RebeccaRGB/K130/Arduino/K130/translate.cpp

#include <Arduino.h>
#include <avr/pgmspace.h>
#include "translate.h"

static const unsigned char translation_table[] PROGMEM = {
  0x29, // 0x00 -> 0x29 esc
  0x35, // 0x01 -> 0x35 ` ~
  0x2B, // 0x02 -> 0x2B tab
  0x39, // 0x03 -> 0x39 caps lock
  0xE1, // 0x04 -> 0xE1 left shift
  0xE0, // 0x05 -> 0xE0 left ctrl
  0x85, // 0x06 -> 0x85 numpad ,
  0x59, // 0x07 -> 0x59 numpad 1
  0x5D, // 0x08 -> 0x5D numpad 5
  0x60, // 0x09 -> 0x60 numpad 8
  0x67, // 0x0A -> 0x67 numpad =
  0x81, // 0x0B -> 0x81 volume down
  0x69, // 0x0C -> 0x69 F14
  0x6B, // 0x0D -> 0x6B F16
  0x6D, // 0x0E -> 0x6D F18
  0x6F, // 0x0F -> 0x6F F20
  0x71, // 0x10 -> 0x71 F22
  0x73, // 0x11 -> 0x73 F24
  0x63, // 0x12 -> 0x63 numpad .
  0x5A, // 0x13 -> 0x5A numpad 2
  0x5E, // 0x14 -> 0x5E numpad 6
  0x61, // 0x15 -> 0x61 numpad 9
  0x54, // 0x16 -> 0x54 numpad /
  0x80, // 0x17 -> 0x80 volume up
  0x68, // 0x18 -> 0x68 F13
  0x6A, // 0x19 -> 0x6A F15
  0x6C, // 0x1A -> 0x6C F17
  0x6E, // 0x1B -> 0x6E F19
  0x70, // 0x1C -> 0x70 F21
  0x72, // 0x1D -> 0x72 F23
  0x58, // 0x1E -> 0x58 numpad enter
  0x5B, // 0x1F -> 0x5B numpad 3
  0x57, // 0x20 -> 0x57 numpad +
  0x56, // 0x21 -> 0x56 numpad -
  0x55, // 0x22 -> 0x55 numpad *
  0x66, // 0x23 -> 0x66 power
  0x3A, // 0x24 -> 0x3A F1
  0x1E, // 0x25 -> 0x1E 1 !
  0x14, // 0x26 -> 0x14 Q
  0x04, // 0x27 -> 0x04 A
  0x64, // 0x28 -> 0x64 ISO \ |
  0x01, // 0x29 -> 0x01 fn
  0x62, // 0x2A -> 0x62 numpad 0
  0x52, // 0x2B -> 0x52 up arrow
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
};

unsigned char translate_scancode(unsigned char packet) {
  return pgm_read_byte(&translation_table[packet]);
}

unsigned int translate_packet(unsigned int packet) {
  unsigned char scancode = translate_scancode(packet);
  return scancode ? ((packet &~ 0xFF) | scancode) : 0;
}
