RebeccaRGB/K130/Arduino/K130/switches.h

#ifndef __SWITCHES_H__
#define __SWITCHES_H__

#define SWITCH_1  26
#define SWITCH_2  27
#define SWITCH_3  28
#define SWITCH_4  29
#define SWITCH_5  30
#define SWITCH_6  31

void switches_init();
unsigned char switches_read();

#endif
